DusanF/STM32-nixie-clock/Nixie_clock/Core/Inc/nixie.h

/*
 * nixie.h
 *
 *  Created on: Nov 10, 2020
 *      Author: DusanF
 */

#ifndef INC_NIXIE_H_
#define INC_NIXIE_H_

void nixie_display(uint8_t *disp);
void nixie_cpp(uint8_t *start, uint8_t *end);

#endif /* INC_NIXIE_H_ */
